sparkfun/SparkFun_Digi_XBee_Regulated_Qwiic/docs/assets/imgs/22032/Resized/22032- XBee Explorer Regulated- 02 HIGH RES.jpg

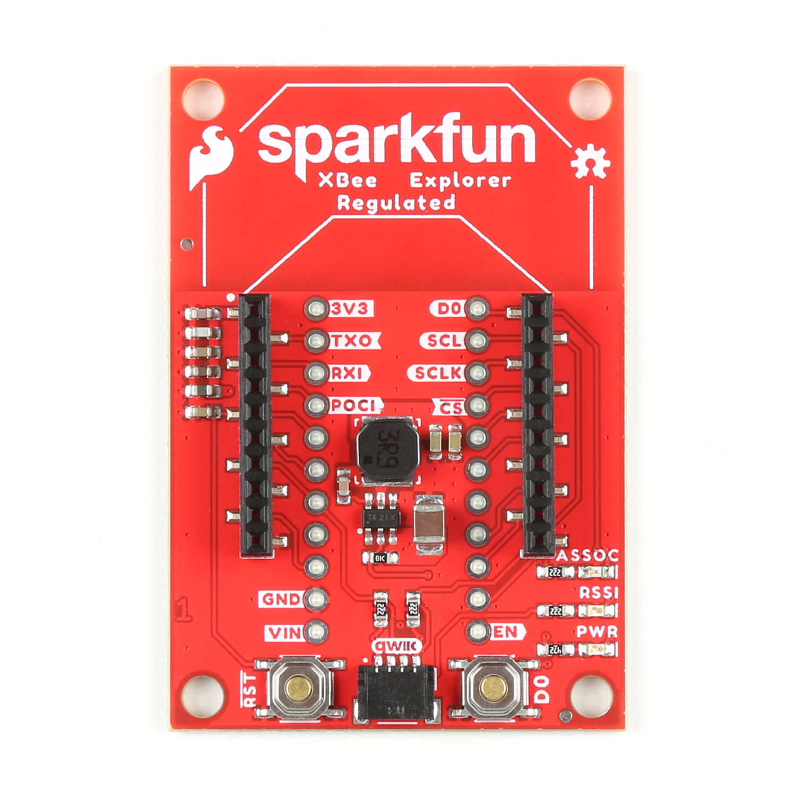
docs/assets/imgs/22032/Resized/22032- XBee Explorer Regulated- 02 HIGH RES.jpg
